paco7828/CompactIRReceiver/showcase/compactirreceiver3.jpg

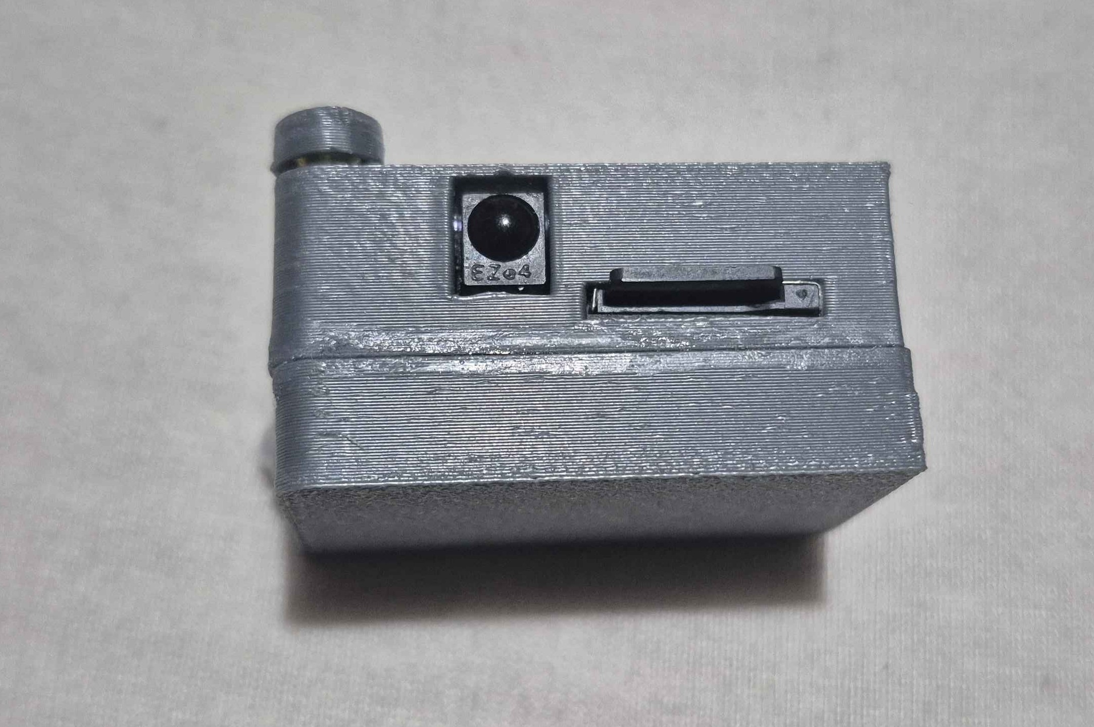
showcase/compactirreceiver3.jpg
