paco7828/CompactIRReceiver/showcase/CompactIRReceiver-proto-bot.jpg

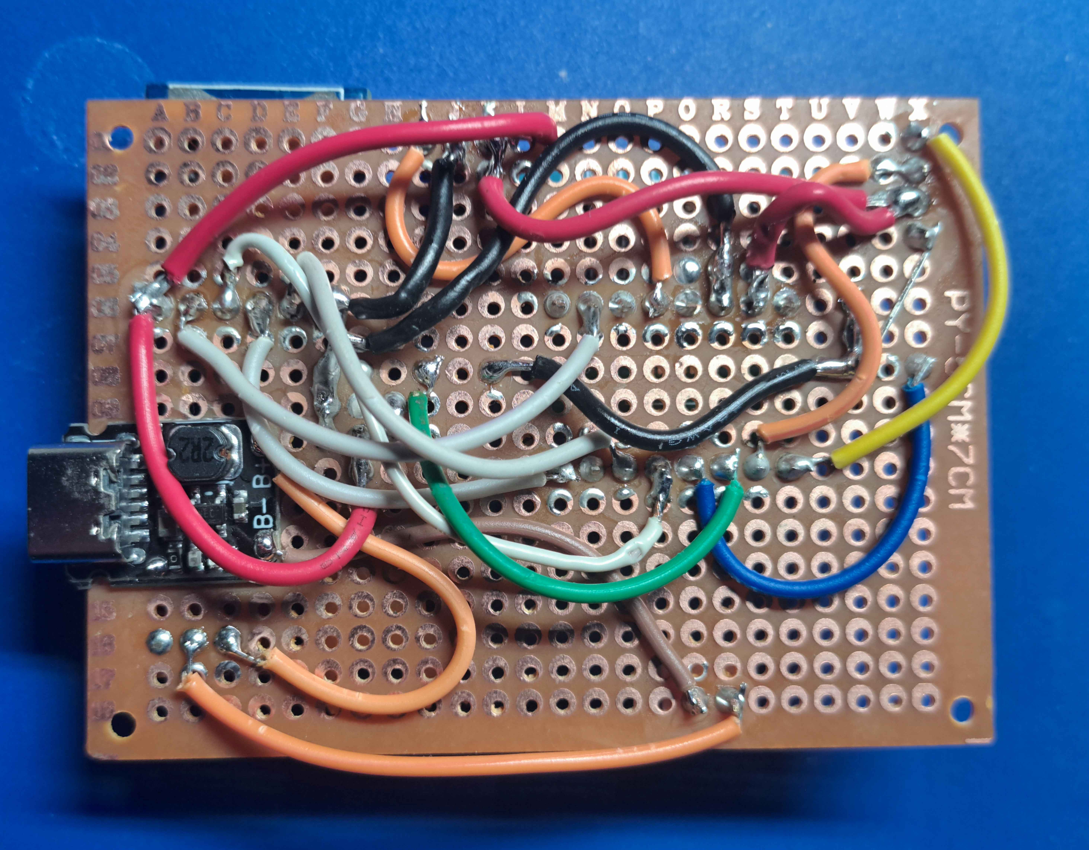
showcase/CompactIRReceiver-proto-bot.jpg
