paco7828/CompactIRReceiver/showcase/CompactIRReceiver-proto-top.jpg

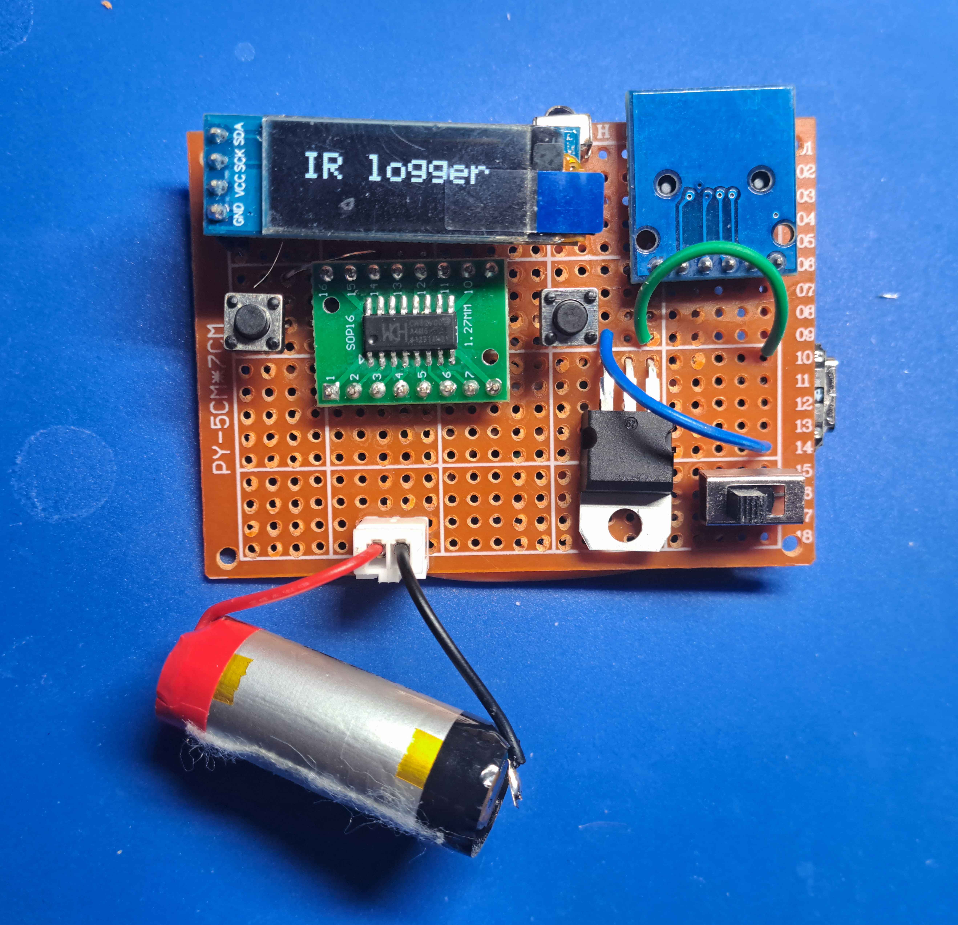
showcase/CompactIRReceiver-proto-top.jpg
